Sweedy3960/2414_SPB7_DOC/Doc/others/CalculRTC.docx

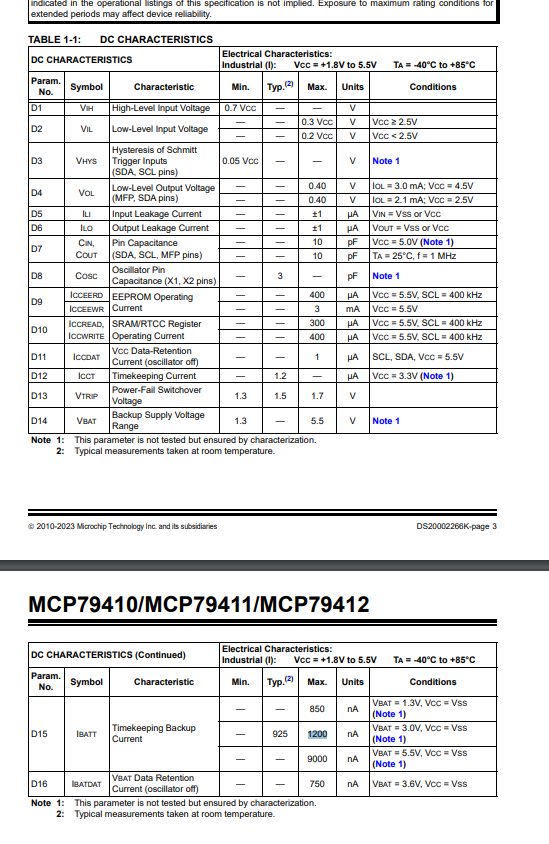
[picture p1: figure]

- Vcap : 1.8 -> 3,3 = 1,5V en 5tau le condo doit diminuer de 1,5V

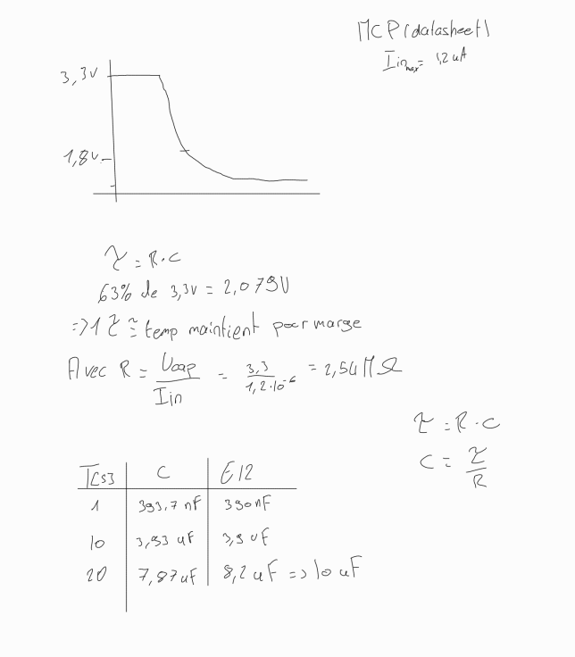
[picture p2: figure]
