Sweedy3960/2414_SPB7_DOC/Doc/others/Capacitive_touch.docx

Rapport de laboratoire

Ecole supérieure

Électronique

Réalisé par :

Aymeric Clauzel

À l’attention de :

Philippe Bovey

Serge Castoldi

Dates :

Début du laboratoire : 5 mars 2024

Fin du laboratoire : 16 avril 2024

Table des matières :

Aucune entrée de table des matières n'a été trouvée.

Sans boitier

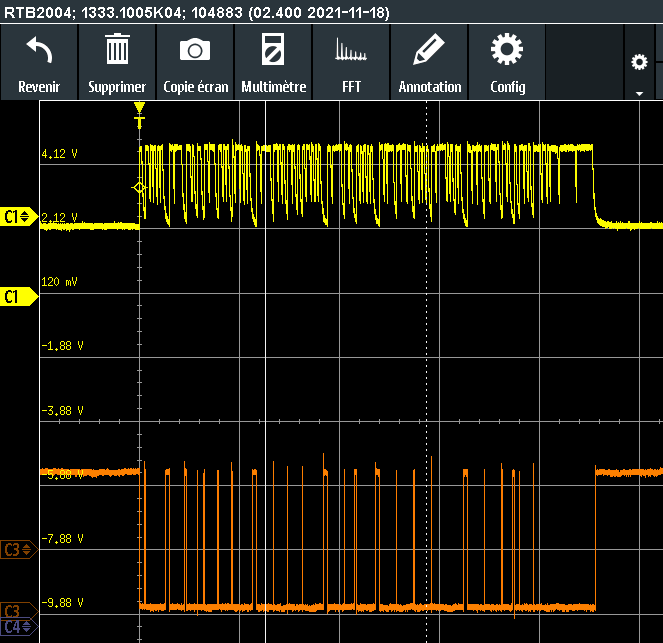
[picture p33: figure]
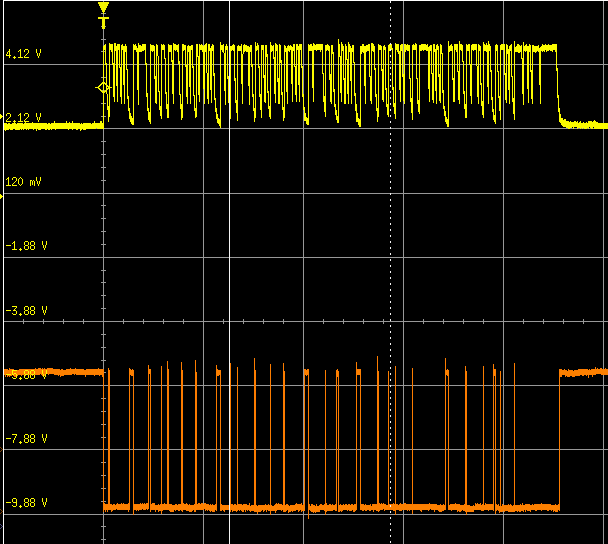
[picture p34: figure]

Pas appuyé | Appuyé

Avec boitier

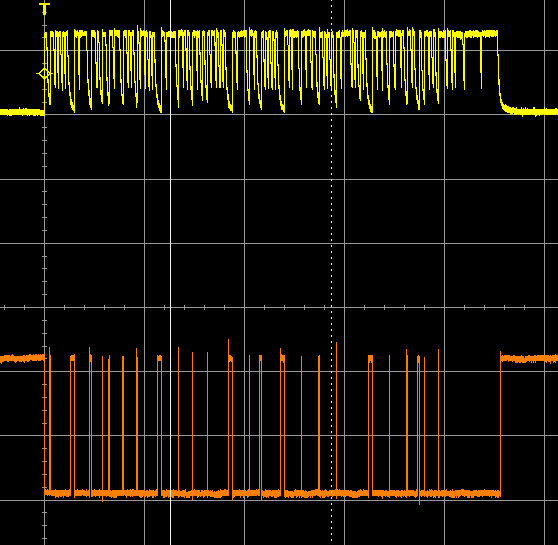
[picture p35: figure]
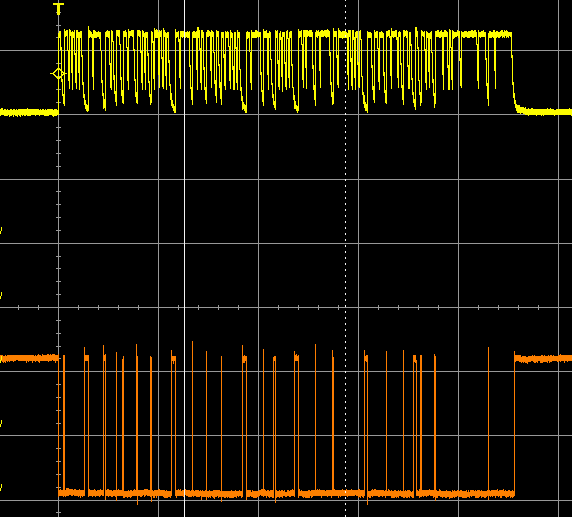
[picture p36: figure]

ACL/NBN Page 1

ETML TP0-LedAd MIN

ETML-Es Modulation FM ELCO
