Sweedy3960/2414_SPB7_DOC/hard/Footprint/ZVP4525ZTA/AltiumDesigner/SOT-89-3_4P5X2P6_DIO.step

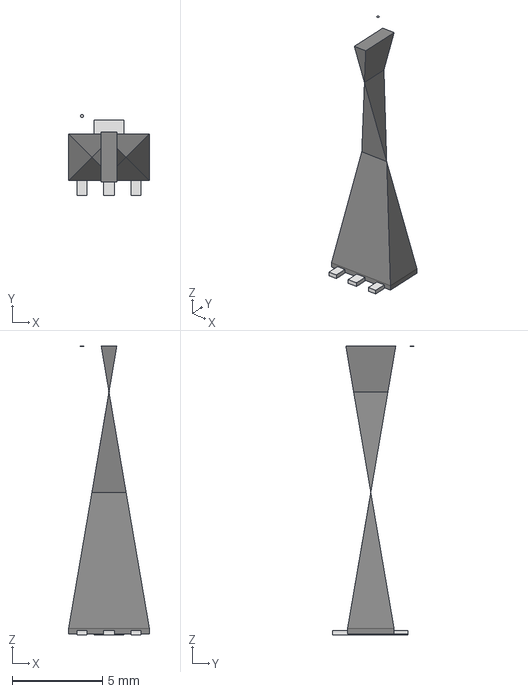
[picture p50: CAD file, 2025-05-13]
hard/Footprint/ZVP4525ZTA/AltiumDesigner/SOT-89-3_4P5X2P6_DIO.step
4.50 x 4.51 x 16.1 mm
