Sweedy3960/2414_SPB7_DOC/Mec/test capa.step

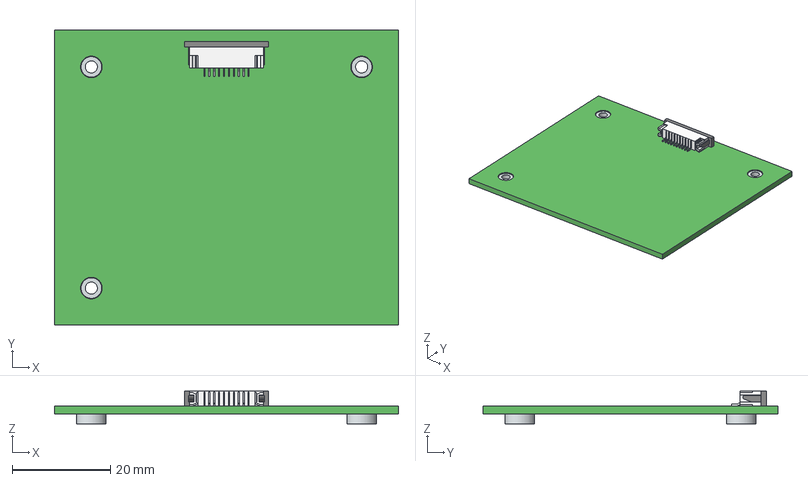
[picture p51: CAD file, 2025-05-13]
Mec/test capa.step
70.0 x 60.0 x 6.63 mm
Geh㴳e_10
Verschluss_10
Pin1 x 10
Pin_rechts
Pin_rechts_mir
