Sweedy3960/2414_SPB7_DOC/Mec/testafrfr.DXF

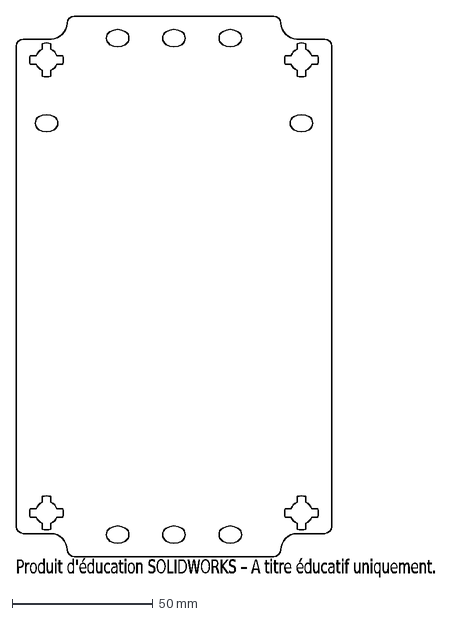
[picture p52: CAD file, 2025-05-13]
Mec/testafrfr.DXF
Produit d'éducation SOLIDWORKS – A titre éducatif uniquement.
