Sweedy3960/2414_SPB7_DOC/Mec/2414_TouchCapa.step

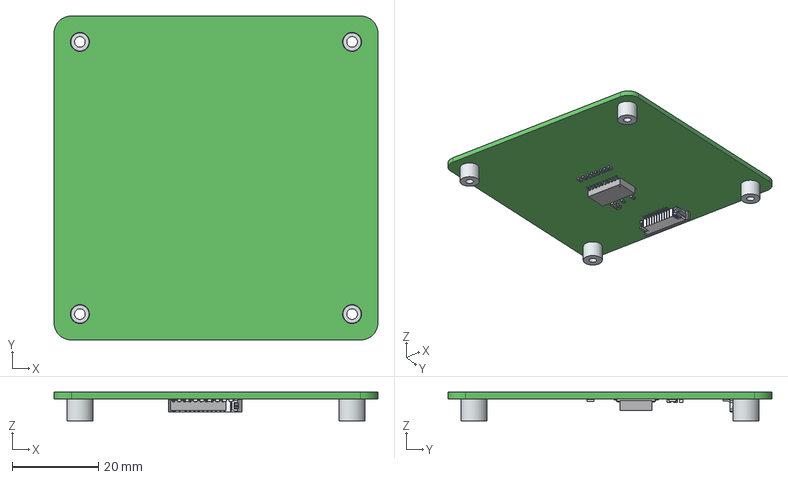
[picture p53: CAD file, 2025-05-13]
Mec/2414_TouchCapa.step
75.0 x 75.0 x 6.61 mm
Mid_Body x 10
Mark x 10
Geh㴳e_10
Verschluss_10
Pin1 x 10
Pin_rechts
Pin_rechts_mir
