Sweedy3960/2414_SPB7_DOC/Mec/PN-1334.STEP

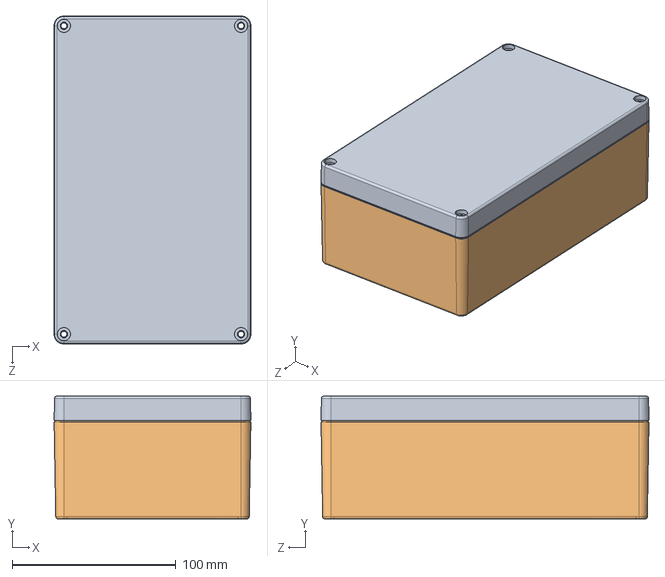
[picture p54: CAD file, 2025-05-13]
Mec/PN-1334.STEP
120.0 x 75.0 x 200.0 mm
1334-C
1334-B
