Sweedy3960/2414_SPB7_DOC/Doc/Project Outputs for 2414_TesteurDeSprinkler_SPB7/DesignDocs/2414_TesteurDeSprinkler_SPB7_Schematic_Variant_No Variations.PDF

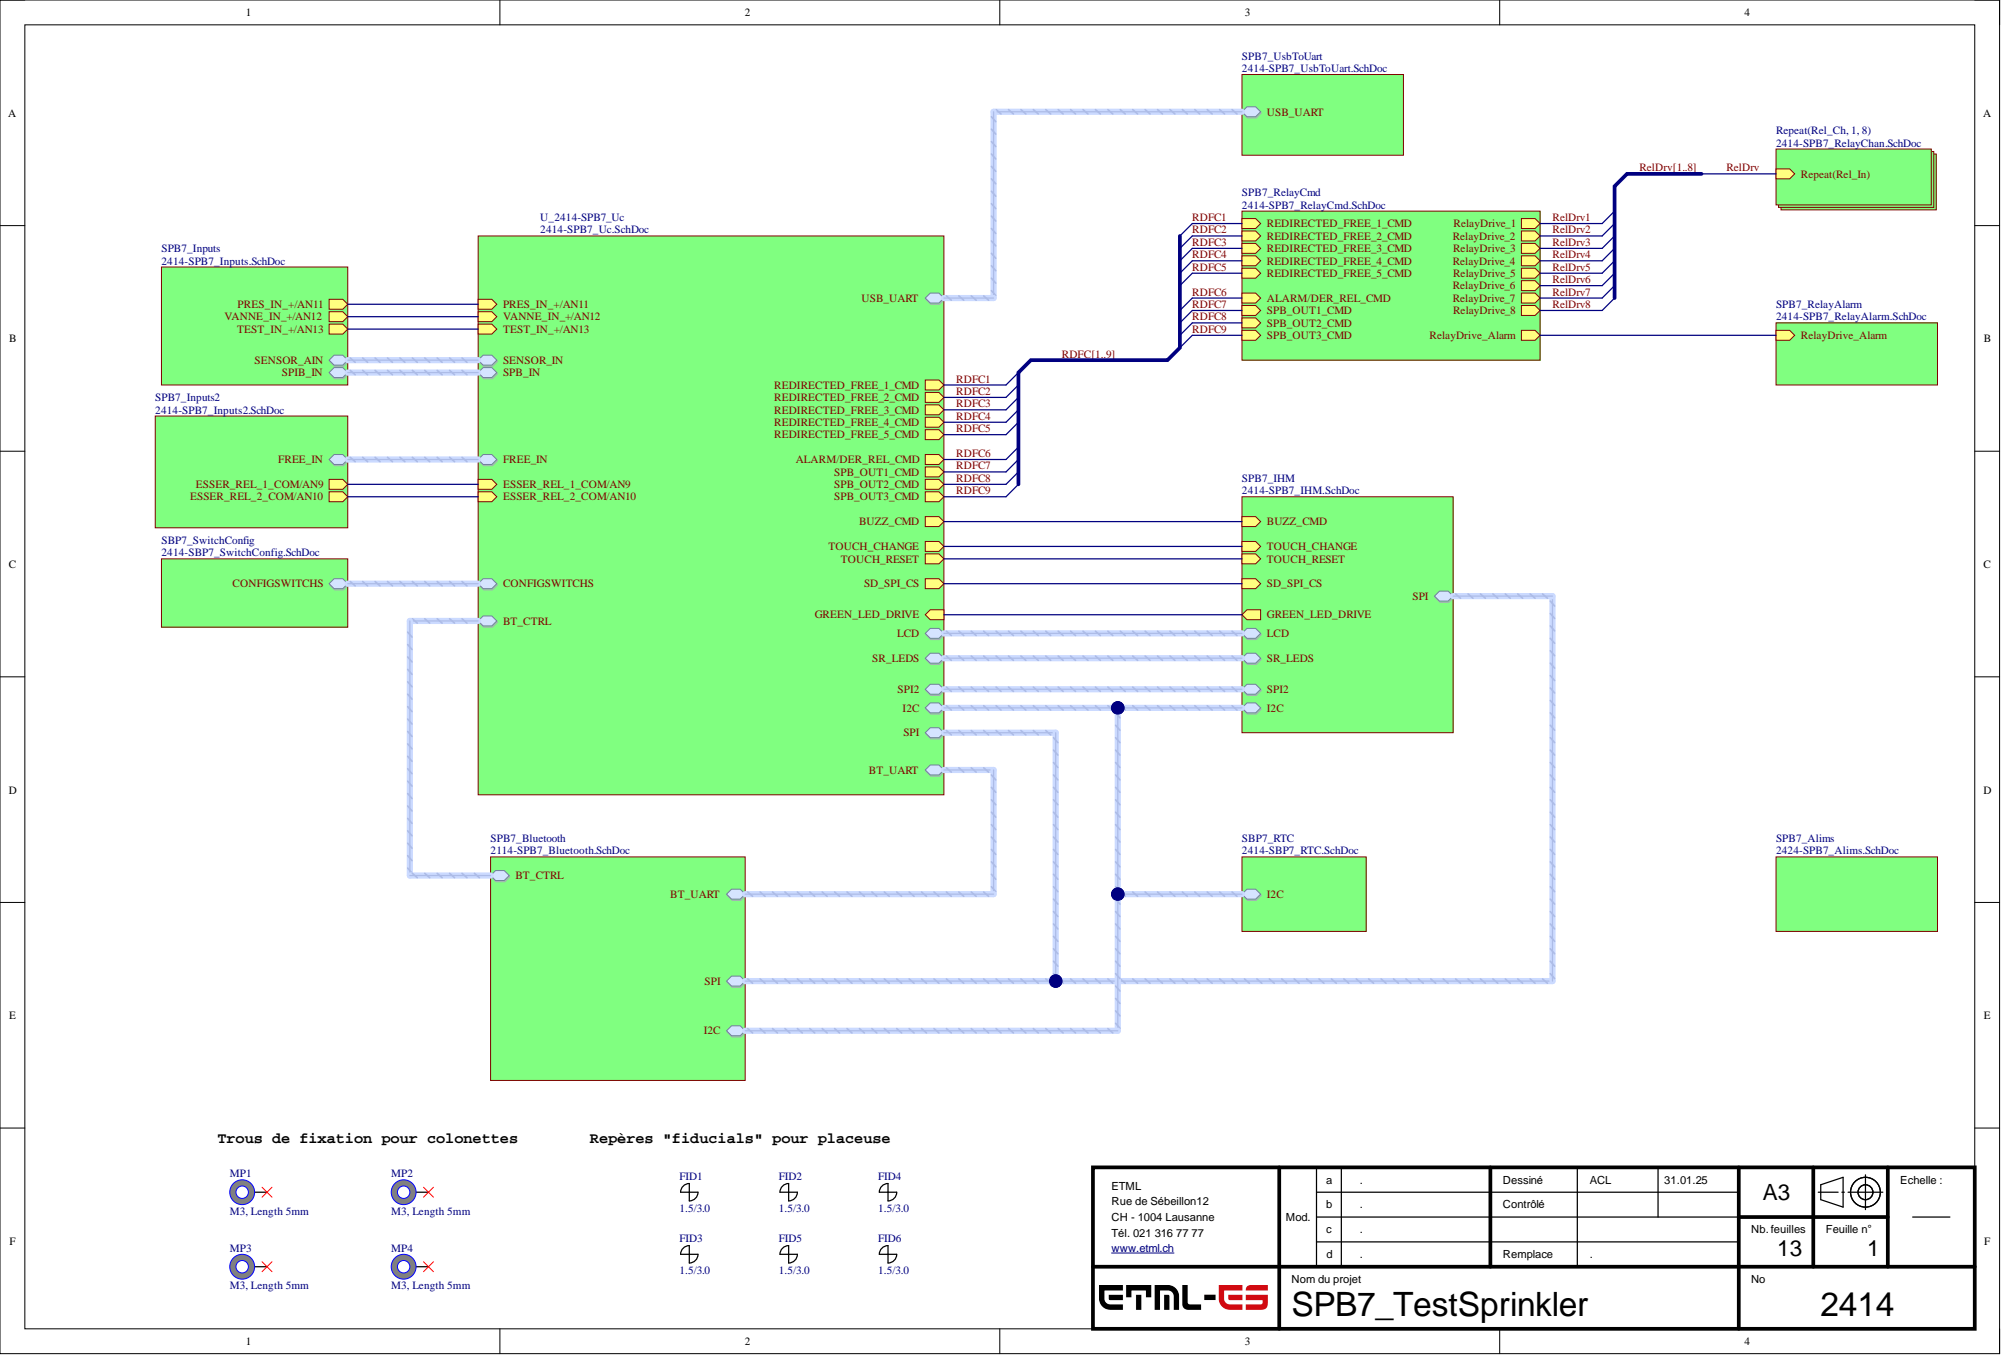
[picture p108: page 1]

ETML Rue de Sébeillon12 CH - 1004 Lausanne Tél. 021 316 77 77 www.etml.ch | Mod. | a | . | Dessiné | ACL | 31.01.25 | A3 | | Echelle :

b | . | Contrôlé

c | . | | | | Nb. feuilles 13 | Feuille n° 1

d | . | Remplace | .

Nom du projet SPB7_TestSprinkler | | | | | | No 2414

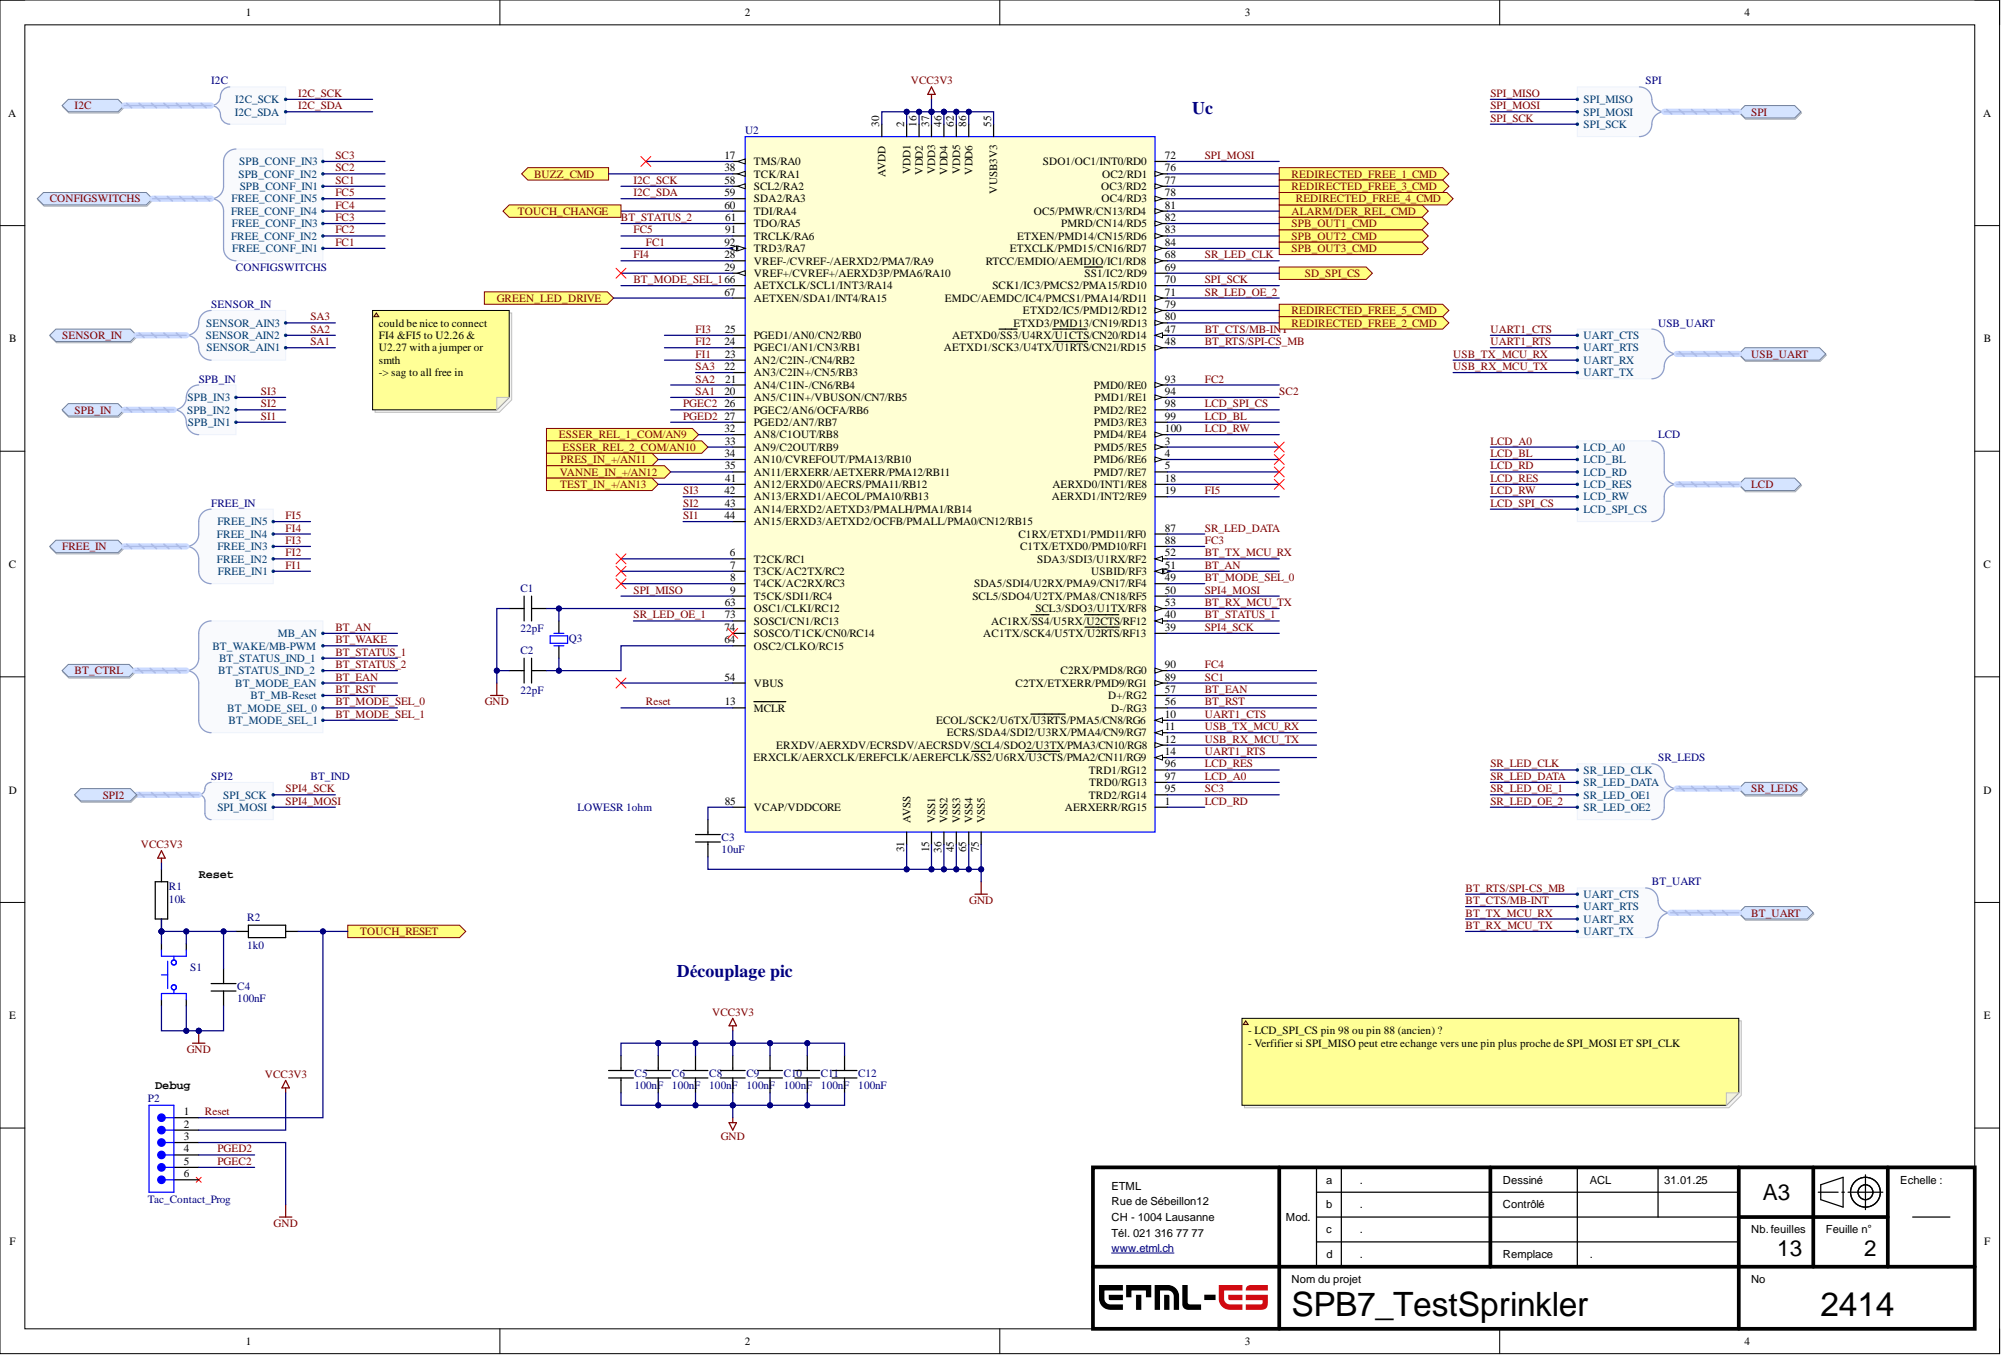
[picture p109: page 2]

ET M L Rue de S ébeillon12 C H - 1004 Lausanne T él. 021 316 77 77 w w w .et m l . c h | Mod . | | | Des s i n é | AC L | 31.01. 2 5 | A3 | | Echelle :

abcd | .... | Cont r ô l é

Nb. feuilles | Feuille n °

Rempla c e | .

Nom du projet SPB7_TestSpr i nkl e r | | | N o 241

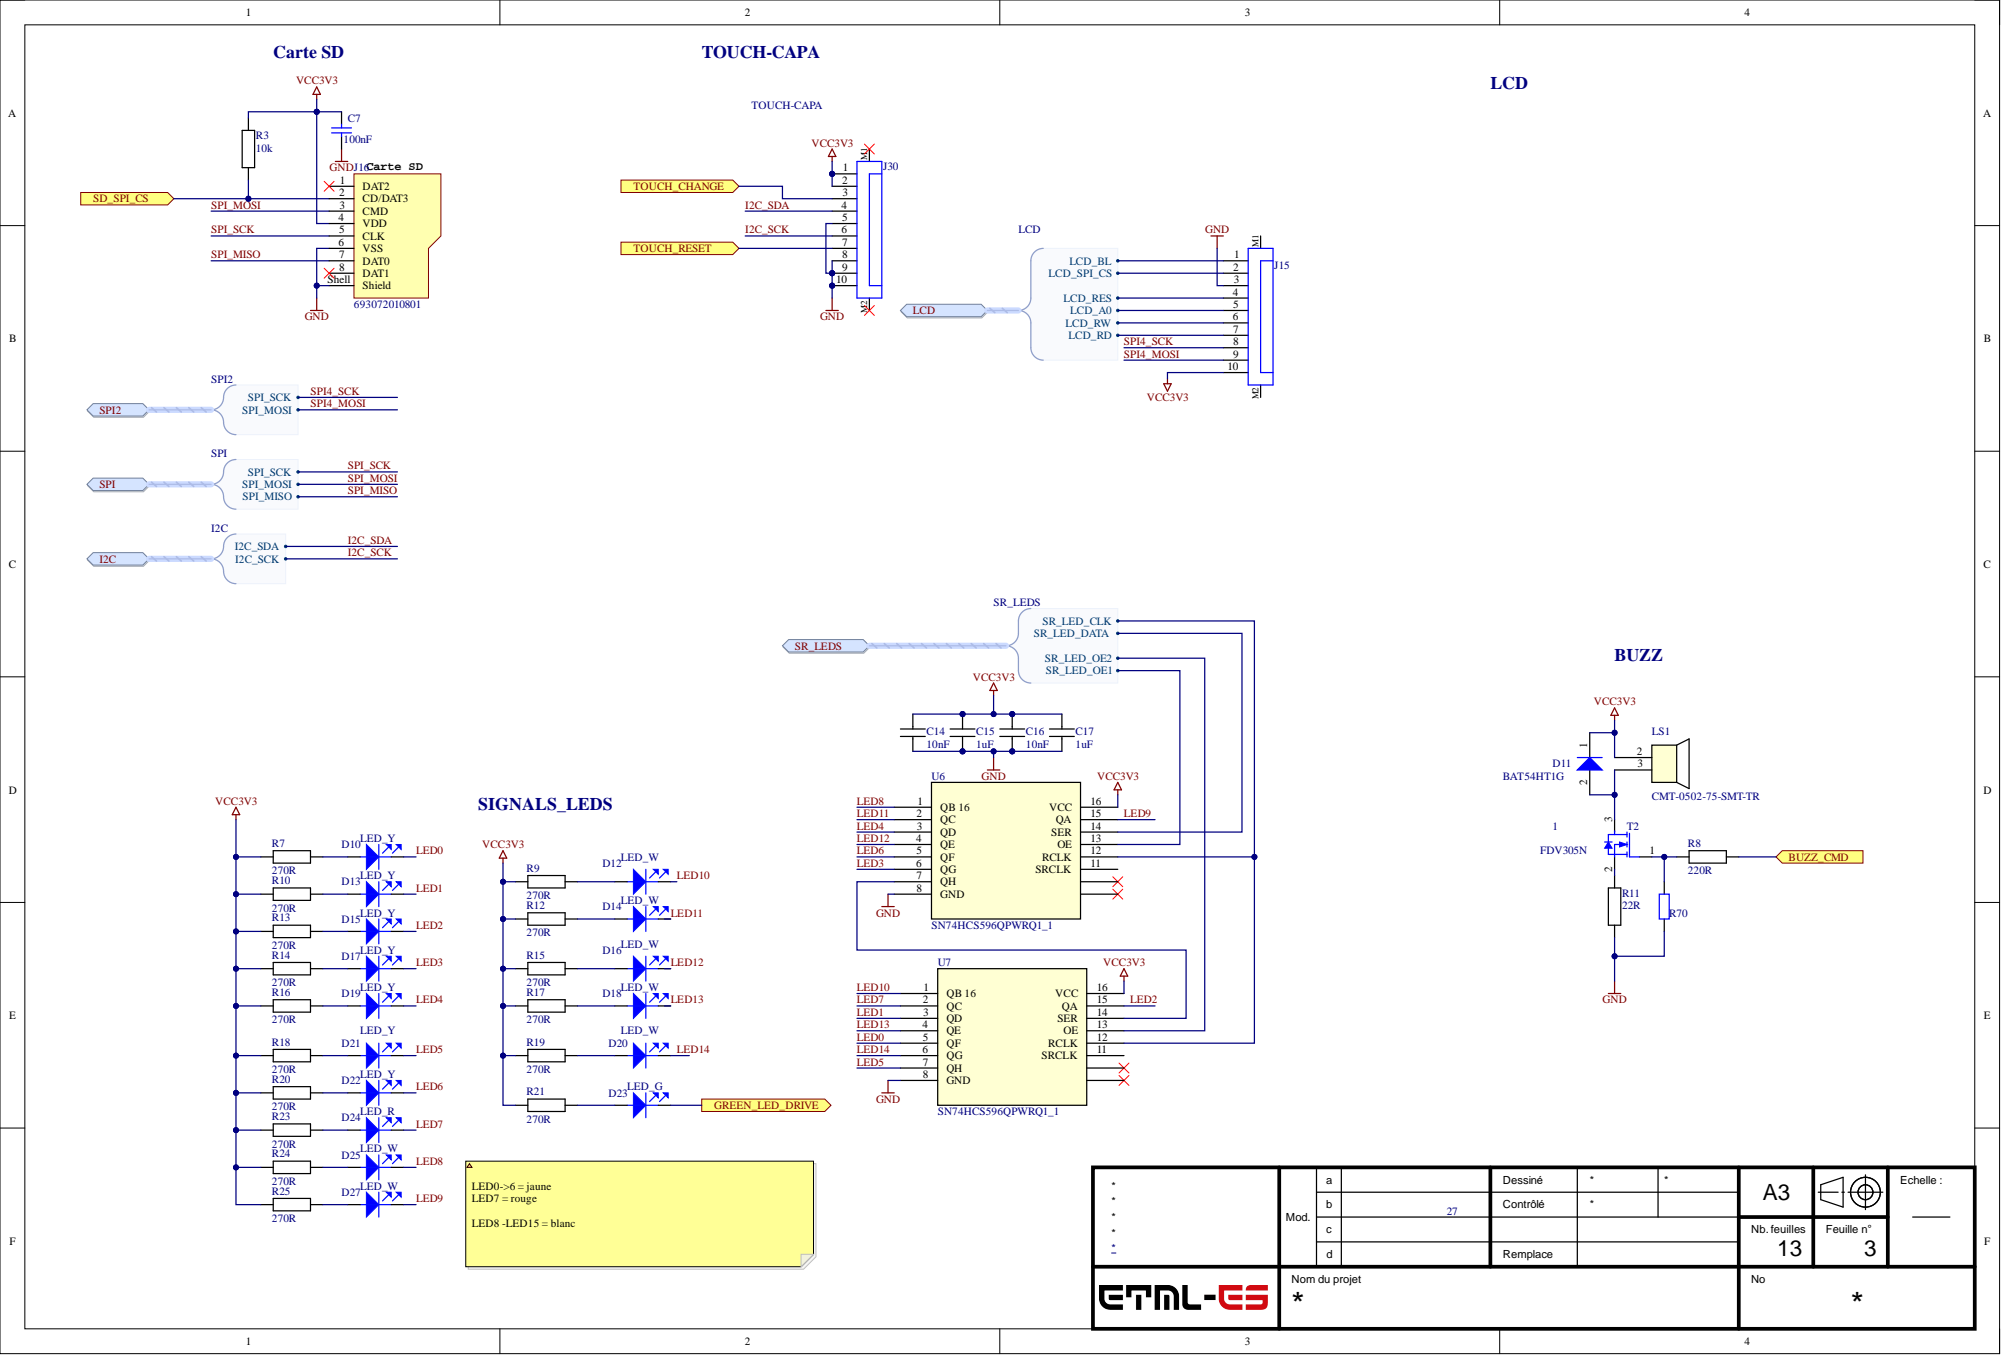
[picture p110: page 3]

* * * * * | Mod. | a | | Dessiné | * | * | A3 | | Echelle :

b | 27 | Contrôlé | *

c | | | | | Nb. feuilles 13 | Feuille n° 3

d | | Remplace

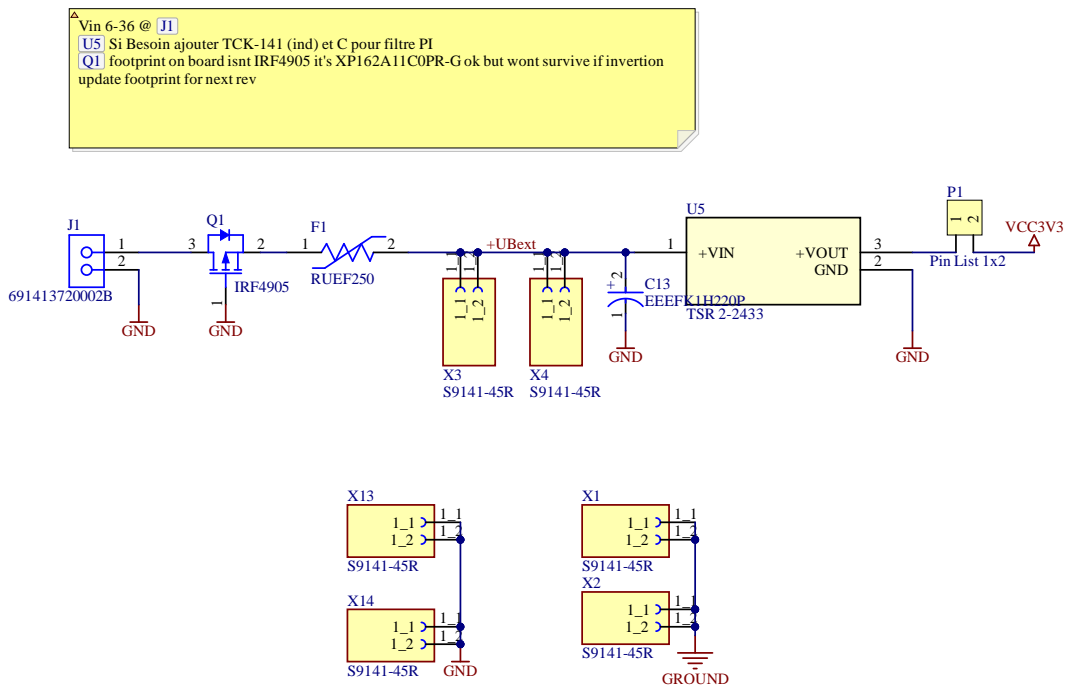
[picture p111: page 4]

Vin 6-36 @ J1
U5 Si Besoin ajouter TCK-141 (ind) et C pour filtre PI
Q1 footprint on board isnt IRF4905 it's XP162A11C0PR-G ok but wont survive if invertion
update footprint for next rev

ETML Rue de Sébeillon12 CH - 1004 Lausanne Tél. 021 316 77 77 www.etml.ch | Mod. | a | . | Dessiné | ACL | 31.01.25 | A4 | | Echelle :

b | . | Contrôlé

c | . | | | | Nb. feuilles 13 | Feuille n° 4

d | . | Remplace | .
SPB7_TestSprinkler | | | | | | 2414

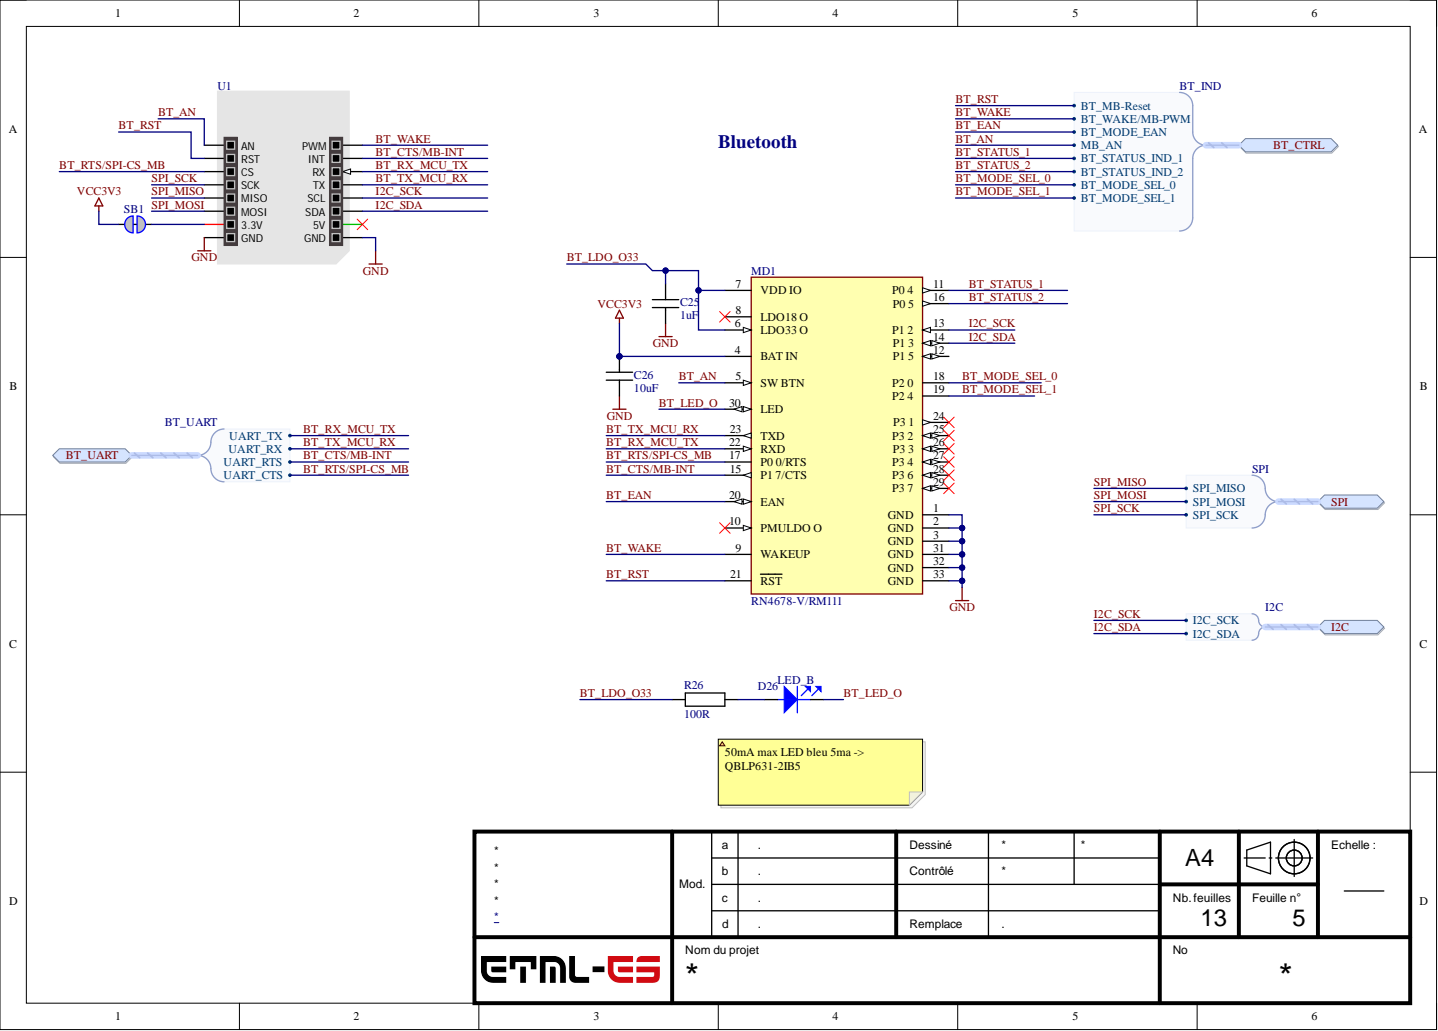
[picture p112: page 5]

* * * * * | Mod. | a | . | Dessiné | * | * | A4 | | Echelle :

b | . | Contrôlé | *

c | . | | | | Nb. feuilles 13 | Feuille n° 5

d | . | Remplace | .

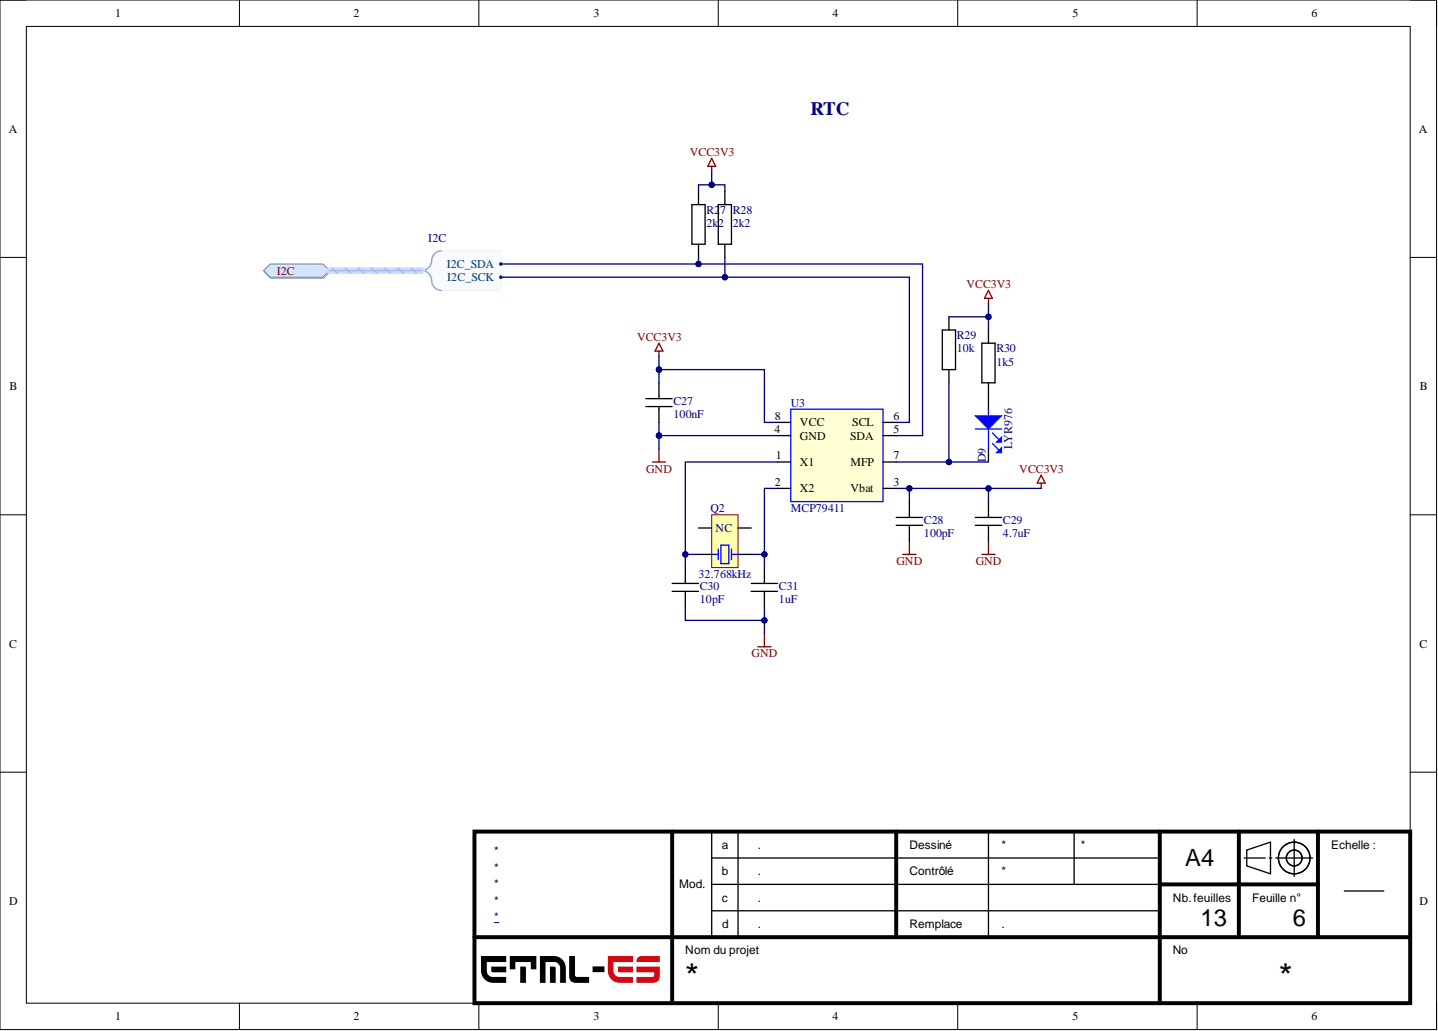
[picture p113: page 6]

3 I2C_SCK

1 | G N D A X 1 MFP X 2 V b at | 7

** *** | Mod . | | | Des s i n é | * | A4 | | Echelle :

abcd | .... | Cont r ô l é

Nb. feuilles 13 | Feuille n ° 6

Rempla c e

Nom du projet * | | N o *

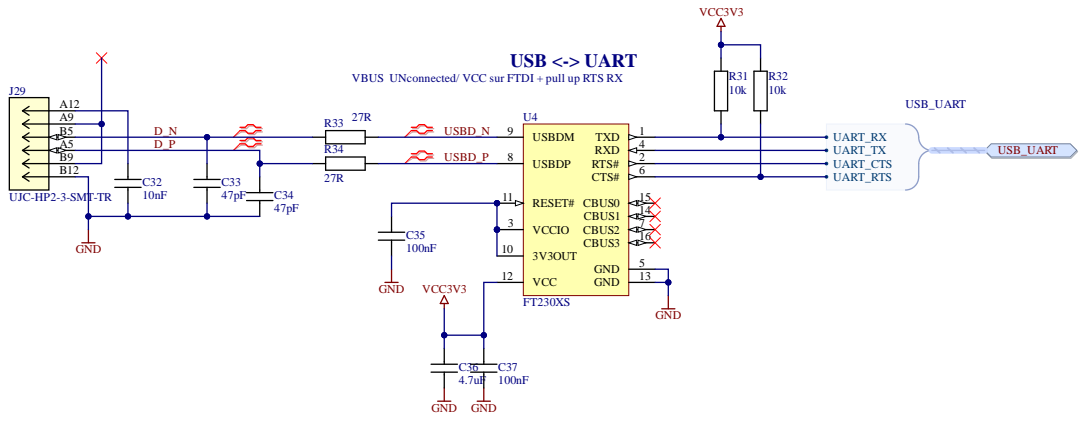
[picture p114: page 7]

** *** | Mod . | | | Des s i n é | * | A4 | | Echelle :

abcd | .... | Cont r ô l é

Nb. feuilles 13 | Feuille n ° 7

Rempla c e

Nom du projet * | | N o *

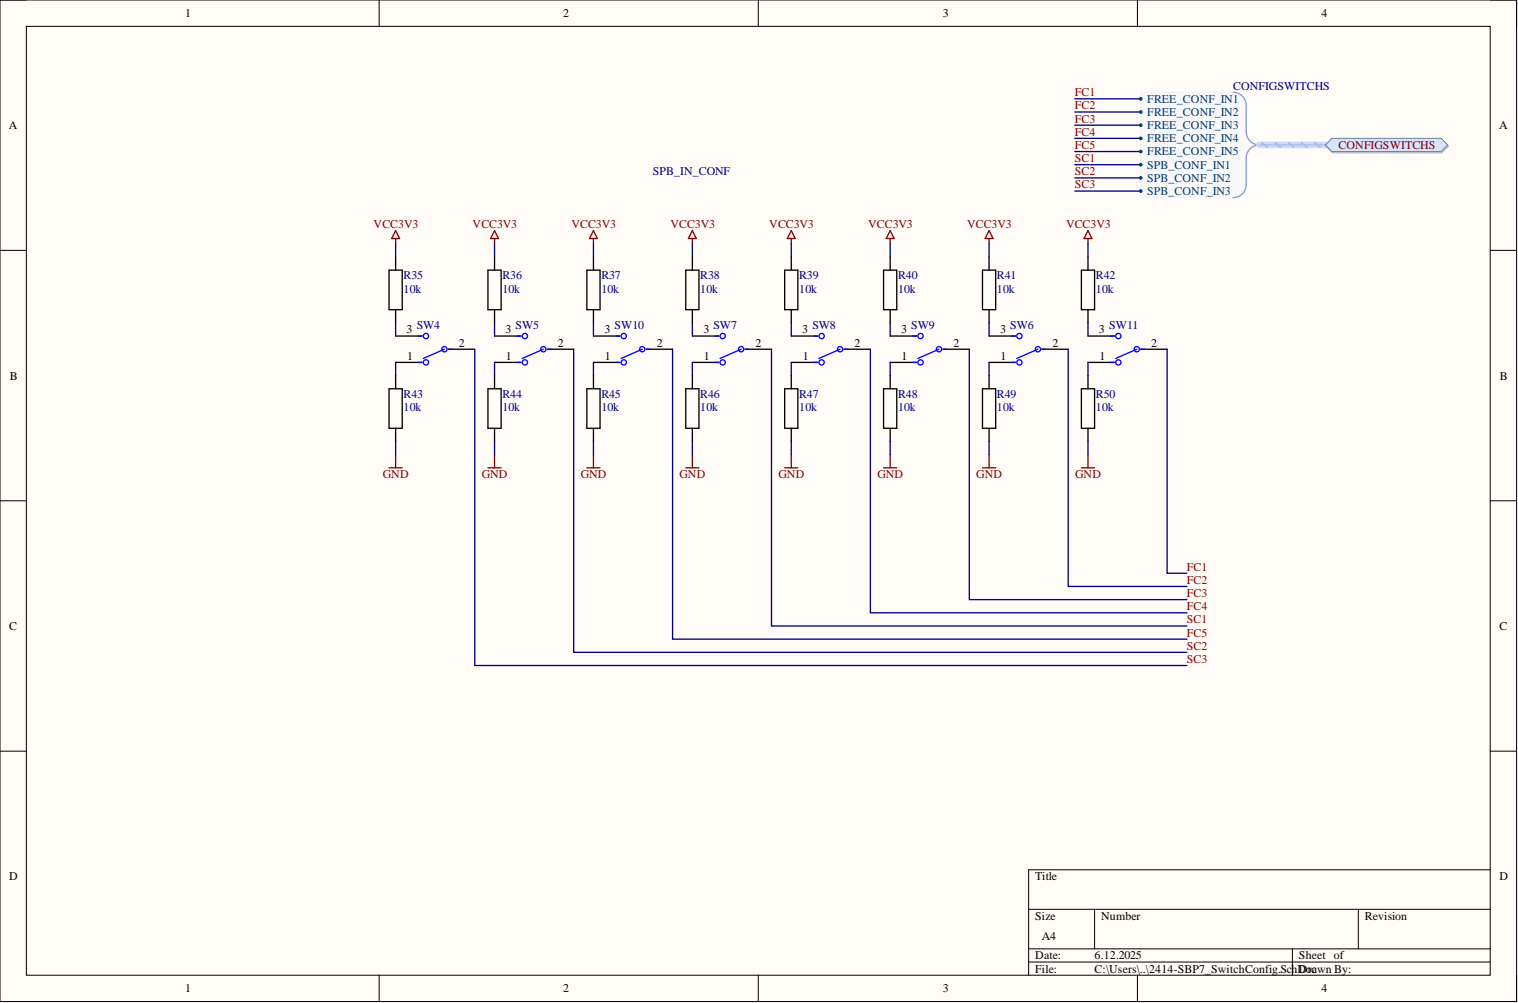
[picture p115: page 8]

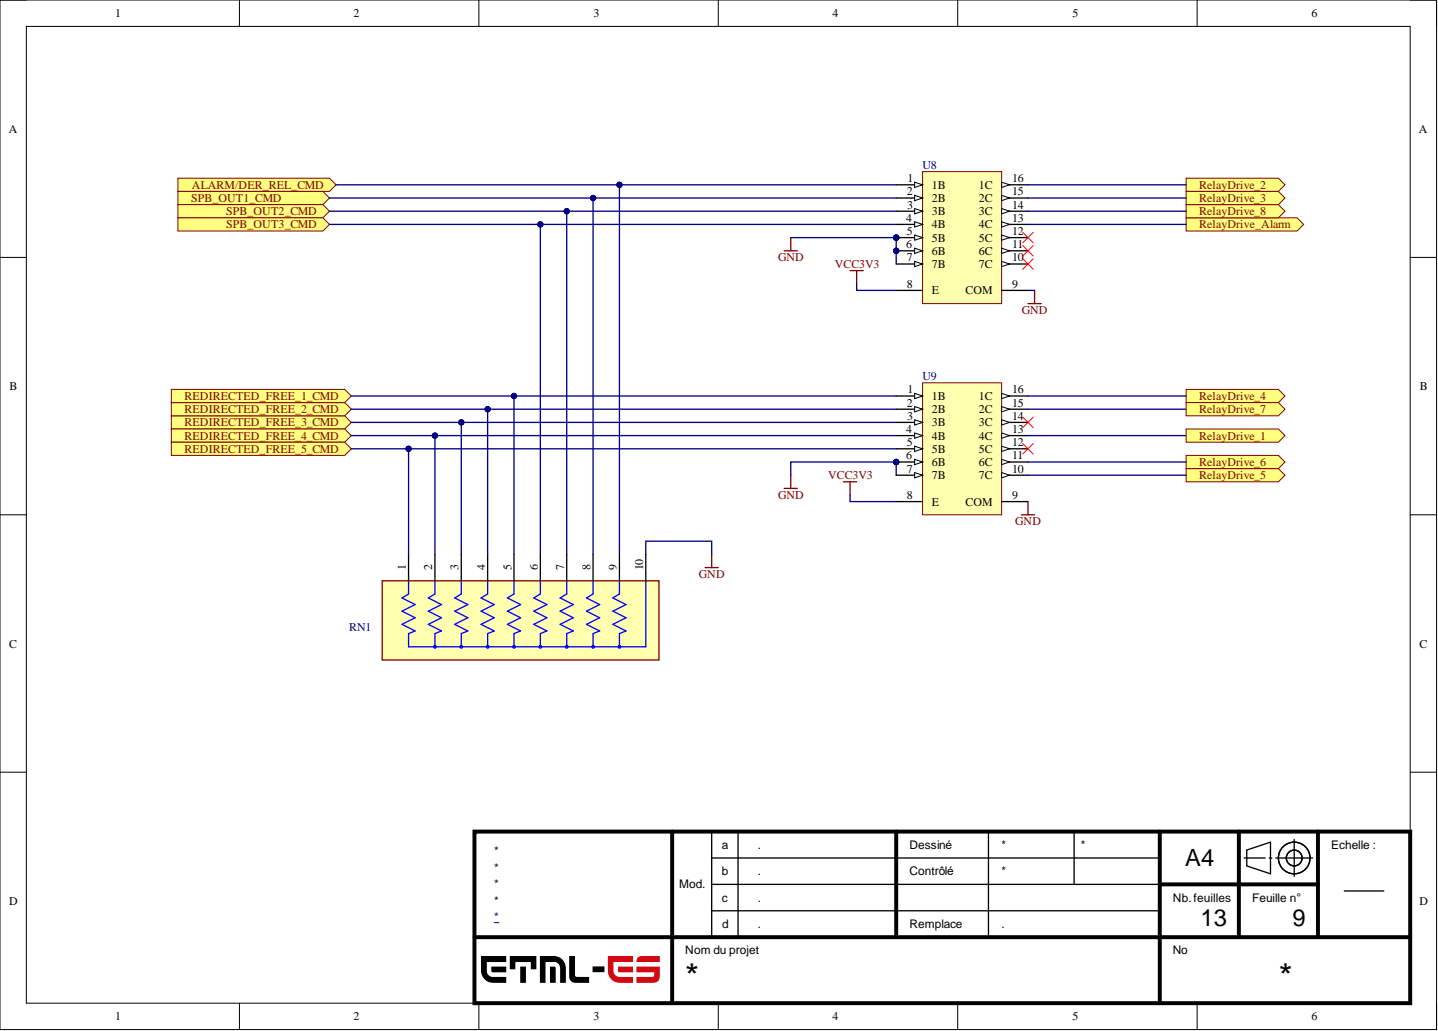
[picture p116: page 9]

* * * * * | Mod. | a | . | Dessiné | * | * | A4 | | Echelle :

b | . | Contrôlé | *

c | . | | | | Nb. feuilles 13 | Feuille n° 9

d | . | Remplace | .

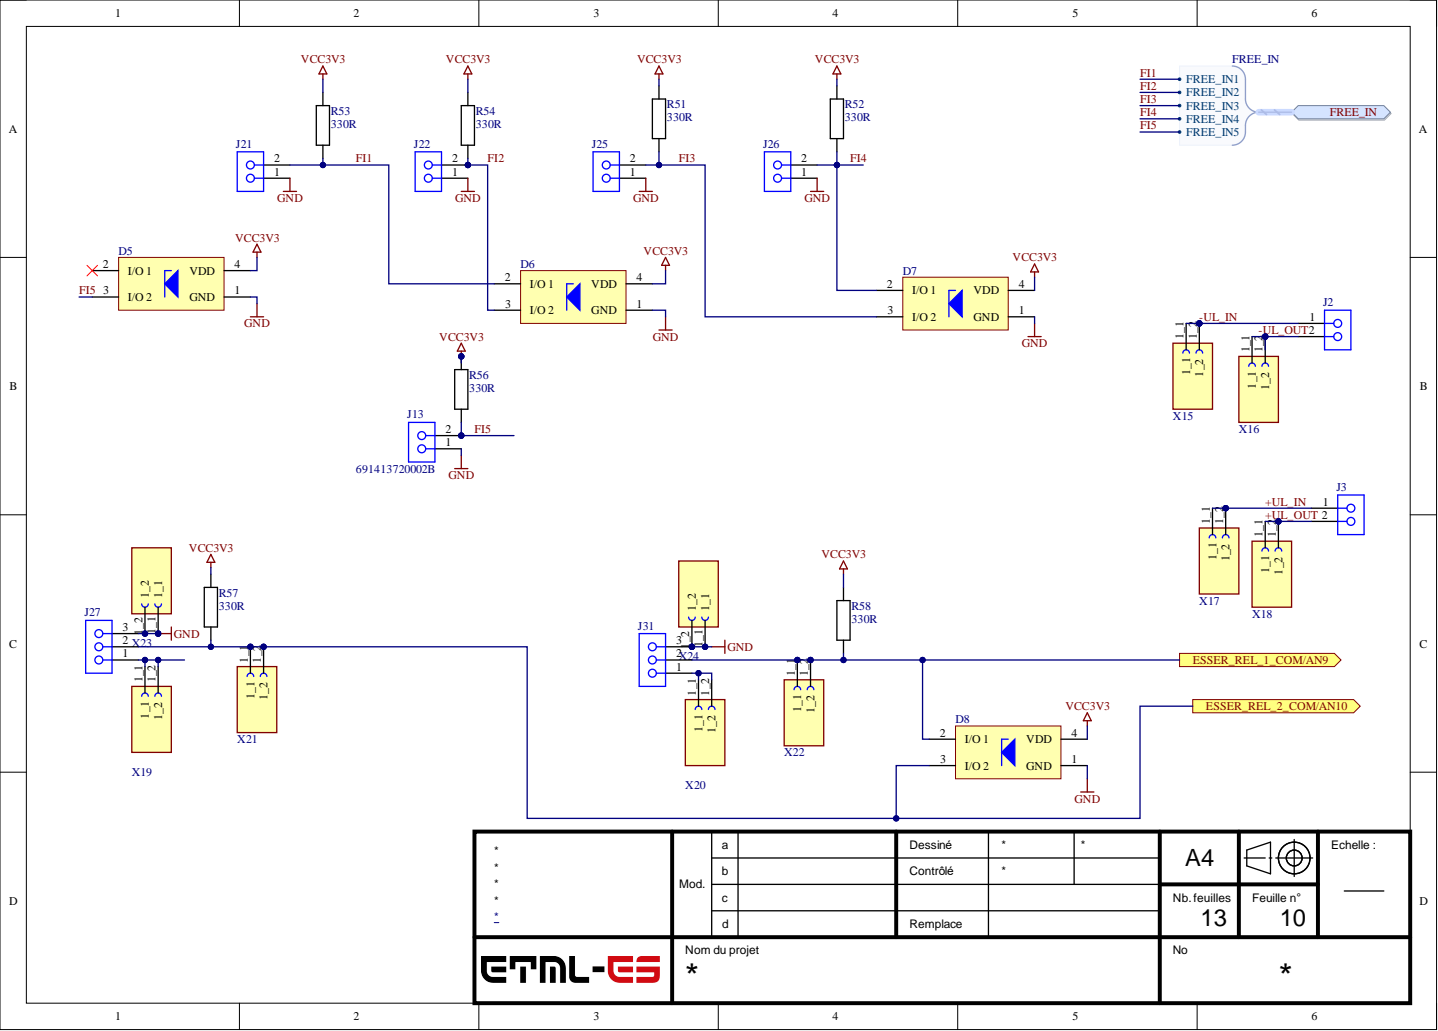
[picture p117: page 10]

-UL_OUT 2

* * * * * | Mod. | a | Dessiné | * | * | A4 | | Echelle :

b | Contrôlé | *

c | | | | Nb. feuilles 13 | Feuille n° 10

d | Remplace

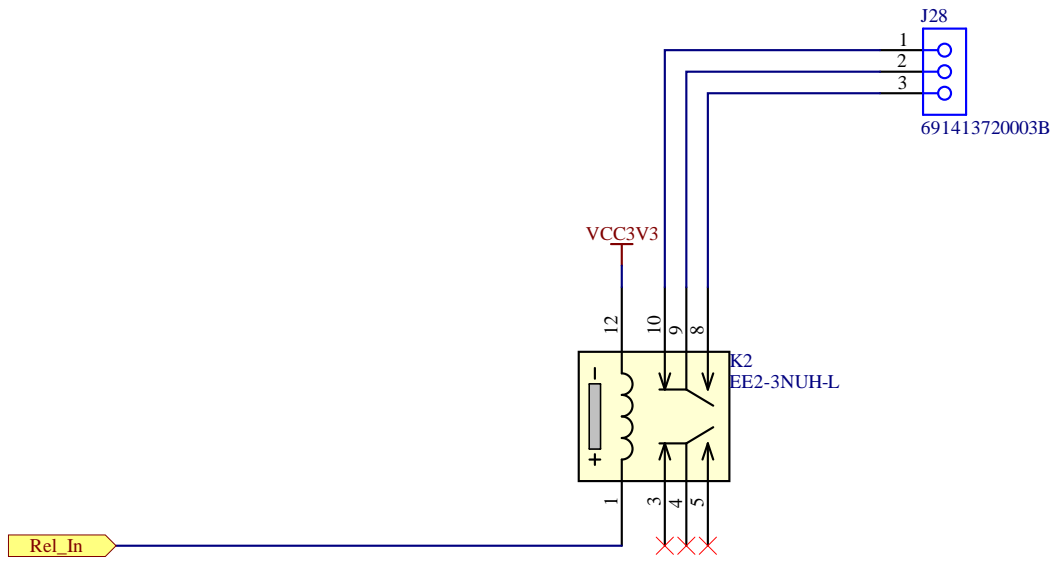
[picture p118: page 11]

** *** | Mod . | | Des s i n é | ** | * | A4 | | Echelle :

abcd | Cont r ô l é

Nb. feuilles 13 | Feuille n ° 1 1

Rempla c e

Nom du projet * | | N o *

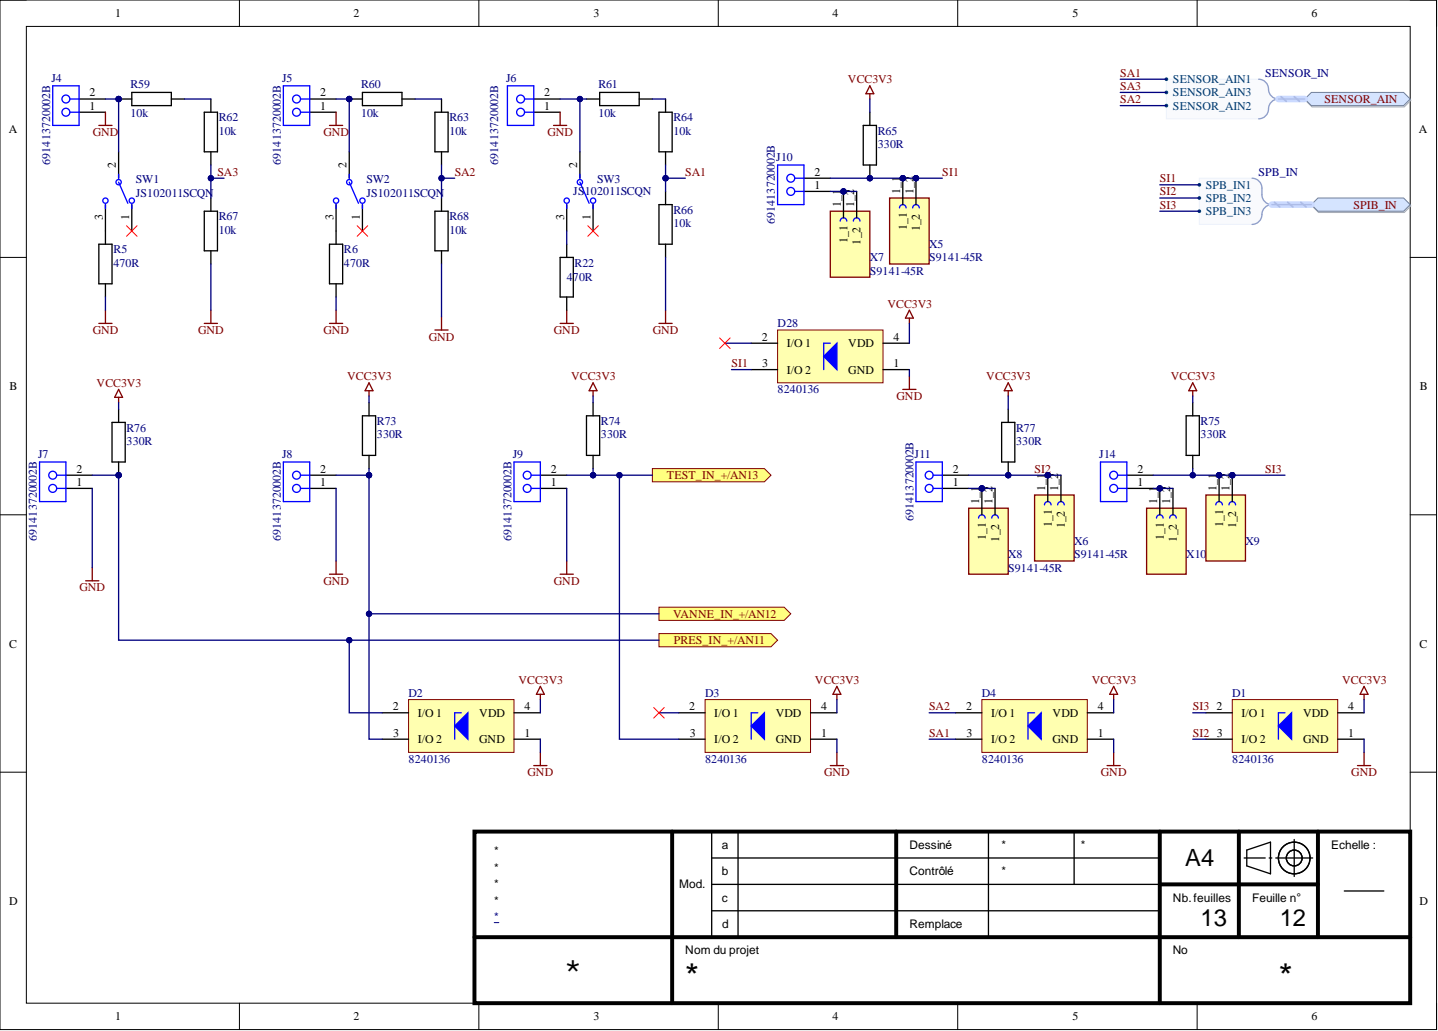
[picture p119: page 12]

* * * * * | Mod. | a | Dessiné | * | * | A4 | | Echelle :

b | Contrôlé | *

c | | | | Nb. feuilles 13 | Feuille n° 12

d | Remplace

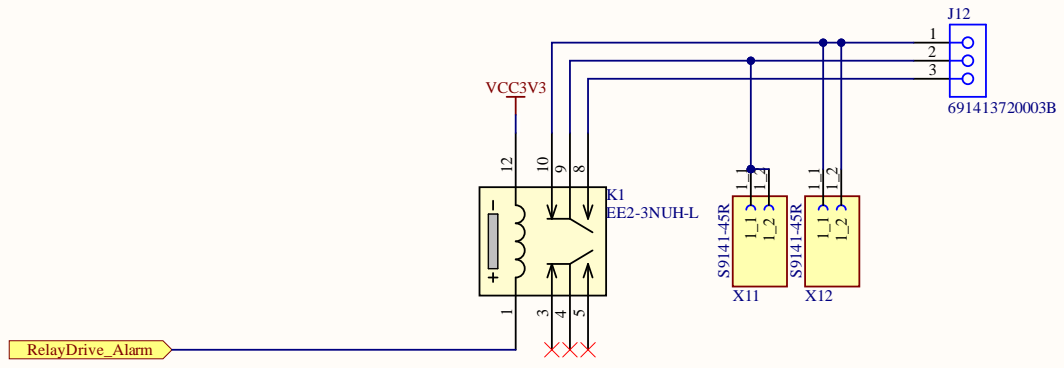
[picture p120: page 13]
