Sweedy3960/2414_SPB7_DOC/Doc/2414_TesteurDeSprinklerplanif.xlsx

No semaine projet |  | 1 | 2 | 3 | 4 | 5 | 6 | V | V | 7 | 8 | 9 | 10 | 11 | 12 | V | 13 | 14 | 15 | 16 | 17 | 18 | 19 | V | V | 20 | 21 | 22 | 23 | V | 24 | 25 | 26 | V
No semaine |  | 47 | 48 | 49 | 50 | 51 | 52 | V | V | 2 | 3 | 4 | 5 | 6 | 7 | V | 9 | 10 | 11 | 12 | 13 | 14 | 15 | V | V | 18 | 20 | 22 | 24 | V | 23 | 24 | 25 | V
Date |  | 2024-11-15 | 2024-11-22 | 2024-11-29 | 2024-12-06 | 2024-12-13 | 2024-12-20 | 2024-12-27 | 2025-01-03 | 2025-01-10 | 2025-01-17 | 2025-01-24 | 2025-01-31 | 2025-02-07 | 2025-02-14 | 2025-02-21 | 2025-02-28 | 2025-03-07 | 2025-03-14 | 2025-03-21 | 2025-03-28 | 2025-04-04 | 2025-04-11 | 2025-04-18 | 2025-04-25 | 2025-05-02 | 2025-05-09 | 2025-05-16 | 2025-05-23 | 2025-05-30 | 2025-06-06 | 2025-06-13 | 2025-06-20 | 2025-06-27
Pré-étude | Consigne |  |  |  | R | P
 | Planifié
 | Réel
Design + Schéma | Consigne |  |  |  |  |  |  |  |  |  |  | R | P
 | Planifié
 | Réel
PCB | Consigne |  |  |  |  |  |  |  |  |  |  |  |  |  |  |  |  |  |  |  | R
 | Planifié
 | Réel
Montage | Consigne |  |  |  |  |  |  |  |  |  |  |  |  |  |  |  |  |  |  |  |  |  |  |  |  |  |  |  |  |  |  |  |  | V
 | Planifié
 | Réel
Softwares | Consigne
 | Planifié
 | Réel
Tests et mise au point | Consigne
 | Planifié
 | Réel
Rédaction du rapport | Consigne
 | Planifié
 | Réel
Préparation présentation + démo | Consigne
 | Planifié
 | Réel
Présentations | Consigne |  |  |  |  |  |  |  |  |  |  |  |  |  |  |  |  |  |  |  |  |  |  |  |  |  |  |  |  |  |  | R | P
 | Planifié
 | Réel
Finitions/corrections/documentation | Consigne
 | Planifié
 | Réel
Projet
2414_TesteurDeSprinkler
Auteur
Aymeric clauzel
Date de création
2024-01-22
