Sweedy3960/2414_SPB7_DOC/Doc/Grille EVALUATION proj v1-1 modèle.xlsx

Génie électrique
Formulaire d'évaluation de projet
Candidat |  | Modèle
Enseignant responsable |  | Serge CASTOLDI
Enseignant assistant |  | José MORENO
 |  |  |  |  |  | coeff.
 |  |  | 1. Pré-étude (0.5) | #DIV/0! |  | 1
 |  |  | 2. Design (0.5) | #DIV/0! |  | 1
 |  |  | 3a. Réalisation hardware (0.5) | #DIV/0! |  | 2
 |  |  | 3b. Réalisation software (0.5) | #DIV/0! |  | 2
 |  |  | 3c. Dossier (0.5) | #DIV/0! |  | 2
 |  |  | 4. Présentation finale (0.5) | #DIV/0! |  | 1
 |  |  | 5. Attitude (0.5) | #DIV/0! |  | 1
 |  |  | Note obtenue (0.1) | #DIV/0!
Prière de remplir tout ou partie des cases vertes svp.
N° | Partie évaluée | Compétence | Indicateur / Critère de réussite |  | Evaluation A, B, C, D |  |  |  |  | Indicateur valide | Nbre pts max | Nbre pts compétence obtenus | Nbre pts compétence maximum | Pourcentage de compétence
1 | Pré-étude : présentation et dossier | 1.1 Capacité à présenter un sujet par oral | Expression : Le candidat s'exprime clairement, avec le bon langage. Compréhension aisée Qualité de la présentation : Moyens utilisés de manière appropriée, temps respecté |  |  |  | 3 | A |  | FALSE |  | 0 | 0 | #DIV/0!
 |  |  |  |  |  |  | 2 | B
 |  |  |  |  |  |  | 1 | C
 |  |  |  |  |  |  | 0 | D
 |  | 1.2 Maîtrise orale du sujet | Contenu technique : Contenu correct, concis, argumentation convaincante, voie présentée envisageable et maîtrisée Réponses aux questions : Le candidat répond clairement et correctement aux questions |  |  |  | 6 | A |  | FALSE
 |  |  |  |  |  |  | 4 | B
 |  |  |  |  |  |  | 2 | C
 |  |  |  |  |  |  | 0 | D
 |  | 1.3 Capacité à présenter un sujet par écrit | Expression : Le candidat s'exprime clairement, avec le bon langage. Compréhension aisée. Qualité du dossier : forme et structure complètes et cohérentes |  |  |  | 3 | A |  | FALSE
 |  |  |  |  |  |  | 2 | B
 |  |  |  |  |  |  | 1 | C
 |  |  |  |  |  |  | 0 | D
 |  | 1.4 Maîtrise écrite du sujet | Qualité du dossier : Contenu correct, concis, argumentation convaincante, voie présentée envisageable et maîtrisée |  |  |  | 9 | A |  | FALSE
 |  |  |  |  |  |  | 6 | B
 |  |  |  |  |  |  | 3 | C
 |  |  |  |  |  |  | 0 | D
 |  | 1.5 Rapidité d'exécution | Travail accompli : Le candidat a fourni une quantité de travail conforme à ce qu'on pouvait raisonnablement attendre de lui. |  |  |  | 3 | A |  | FALSE
 |  |  |  |  |  |  | 2 | B
 |  |  |  |  |  |  | 1 | C
 |  |  |  |  |  |  | 0 | D
 |  | Remarques | 1.1 1.2 1.3 1.4 1.5
N° | Partie évaluée | Compétence | Indicateur / Critère de réussite |  | Evaluation A, B, C, D |  |  |  |  | Indicateur valide | Nbre pts max | Nbre pts compétence obtenus | Nbre pts compétence maximum | Pourcentage de compétence
2 | Design : présentation et dossier | 2.1 Capacité à présenter un sujet par oral | Expression : Le candidat s'exprime clairement, avec le bon langage. Compréhension aisée Qualité de la présentation : Moyens utilisés de manière appropriée, temps respecté |  |  |  | 3 | A |  | FALSE |  | 0 | 0 | #DIV/0!
 |  |  |  |  |  |  | 2 | B
 |  |  |  |  |  |  | 1 | C
 |  |  |  |  |  |  | 0 | D
 |  | 2.2 Maîtrise orale du sujet | Contenu technique : Contenu correct, concis, argumentation convaincante, voie présentée envisageable et maîtrisée Réponses aux questions : Le candidat répond clairement et correctement aux questions |  |  |  | 6 | A |  | FALSE
 |  |  |  |  |  |  | 4 | B
 |  |  |  |  |  |  | 2 | C
 |  |  |  |  |  |  | 0 | D
 |  | 2.3 Capacité à présenter un sujet par écrit | Expression : Le candidat s'exprime clairement, avec le bon langage. Compréhension aisée. Qualité du dossier : forme et structure, contenu complet et cohérent |  |  |  | 3 | A |  | FALSE
 |  |  |  |  |  |  | 2 | B
 |  |  |  |  |  |  | 1 | C
 |  |  |  |  |  |  | 0 | D
 |  | 2.4 Maîtrise écrite du sujet | Qualité du dossier : Contenu correct, concis, argumentation convaincante, voie présentée envisageable et maîtrisée |  |  |  | 9 | A |  | FALSE
 |  |  |  |  |  |  | 6 | B
 |  |  |  |  |  |  | 3 | C
 |  |  |  |  |  |  | 0 | D
 |  | 2.5 Rapidité d'exécution | Travail accompli : Le candidat a fourni une quantité de travail conforme à ce qu'on pouvait raisonnablement attendre de lui. |  |  |  | 3 | A |  | FALSE
 |  |  |  |  |  |  | 2 | B
 |  |  |  |  |  |  | 1 | C
 |  |  |  |  |  |  | 0 | D
 |  | Remarques | 2.1 2.2 2.3 2.4 2.5
N° | Partie évaluée | Compétence | Indicateur / Critère de réussite |  | Evaluation A, B, C, D |  |  |  |  | Indicateur valide | Nbre pts max | Nbre pts compétence obtenus | Nbre pts compétence maximum | Pourcentage de compétence
3a | Réalisation hardware | 3a.1 Réalisation CAO | Qualité professionnelle de la réalisation CAO. Réutilisable. Documenté. Tous les documents permettant la construction d'une pièce sont disponibles. |  |  |  | 3 | A |  | FALSE |  | 0 | 0 | #DIV/0!
 |  |  |  |  |  |  | 2 | B
 |  |  |  |  |  |  | 1 | C
 |  |  |  |  |  |  | 0 | D
 |  | 3a.2 Montage, mise en service, mise au point | Qualité professionnelle du montage (brasures, placement composants, etc). Nombre et importances des modifications, patchs, etc |  |  |  | 3 | A |  | FALSE
 |  |  |  |  |  |  | 2 | B
 |  |  |  |  |  |  | 1 | C
 |  |  |  |  |  |  | 0 | D
 |  | 3a.3 Atteinte des objectifs | Niveau de fonctionnement / Fonctionnalités implementées : Cahier des charges rempli/remplissable avec le hardware présenté. |  |  |  | 3 | A |  | FALSE
 |  |  |  |  |  |  | 2 | B
 |  |  |  |  |  |  | 1 | C
 |  |  |  |  |  |  | 0 | D
 |  | Remarques | 3a.1 3a.2 3a.3
N° | Partie évaluée | Compétence | Indicateur / Critère de réussite |  | Evaluation A, B, C, D |  |  |  |  | Indicateur valide | Nbre pts max | Nbre pts compétence obtenus | Nbre pts compétence maximum | Pourcentage de compétence
3b | Réalisation software | 3b.1 Codage | Qualité professionnelle du codage, algorithmique. (Tous les programmes sont évalués : uC, application PC, autre) |  |  |  | 9 | A |  | FALSE |  | 0 | 0 | #DIV/0!
 |  |  |  |  |  |  | 6 | B
 |  |  |  |  |  |  | 3 | C
 |  |  |  |  |  |  | 0 | D
 |  | 3b.2 Documentation du code | Code réutilisable. Documenté. (Tous les programmes sont évalués : uC, application PC, autre) |  |  |  | 3 | A |  | FALSE
 |  |  |  |  |  |  | 2 | B
 |  |  |  |  |  |  | 1 | C
 |  |  |  |  |  |  | 0 | D
 |  | 3b.3 Atteinte des objectifs | Niveau de fonctionnement / Fonctionnalités implementées : Cahier des charges rempli/remplissable avec le(les) software(s) présenté(s). |  |  |  | 6 | A |  | FALSE
 |  |  |  |  |  |  | 4 | B
 |  |  |  |  |  |  | 2 | C
 |  |  |  |  |  |  | 0 | D
 |  | Remarques | 3b.1 3b.2 3b.3
N° | Partie évaluée | Compétence | Indicateur / Critère de réussite |  | Evaluation A, B, C, D |  |  |  |  | Indicateur valide | Nbre pts max | Nbre pts compétence obtenus | Nbre pts compétence maximum | Pourcentage de compétence
3c | Dossier | 3c.1 Capacité à présenter un sujet par écrit | Expression : Le candidat s'exprime clairement, avec le bon langage. Compréhension aisée. Qualité du dossier : forme et structure, contenu complet (y compris annexes demandées) et cohérent |  |  |  | 6 | A |  | FALSE |  | 0 | 0 | #DIV/0!
 |  |  |  |  |  |  | 4 | B
 |  |  |  |  |  |  | 2 | C
 |  |  |  |  |  |  | 0 | D
 |  | 3c.2 Maîtrise écrite du sujet | Qualité du dossier : Contenu correct, concis, argumentation convaincante, voie présentée maîtrisée |  |  |  | 6 | A |  | FALSE
 |  |  |  |  |  |  | 4 | B
 |  |  |  |  |  |  | 2 | C
 |  |  |  |  |  |  | 0 | D
 |  | 3c.3 Validation du hardware | Les éventuelles modifs. après design sont présentées. Le hardware reçu est testé. Les nouvelles modifs éventuelles sont présentées |  |  |  | 6 | A |  | FALSE
 |  |  |  |  |  |  | 4 | B
 |  |  |  |  |  |  | 2 | C
 |  |  |  |  |  |  | 0 | D
 |  | 3c.4 Description du logiciel | Les fonctionnalités et les grandes lignes du logiciel sont expliquées. Tout protocole utilisé ou créé est décrit. |  |  |  | 6 | A |  | FALSE
 |  |  |  |  |  |  | 4 | B
 |  |  |  |  |  |  | 2 | C
 |  |  |  |  |  |  | 0 | D
 |  | 3c.5 Tests et mesures | ...permettant de valider le fonctionnement. |  |  |  | 6 | A |  | FALSE
 |  |  |  |  |  |  | 4 | B
 |  |  |  |  |  |  | 2 | C
 |  |  |  |  |  |  | 0 | D
 |  | 3c.6 Bilan du fonctionnement et conclusion | Un état des lieux est dressé. Il est exhaustif. La reprise du projet est possible. |  |  |  | 3 | A |  | FALSE
 |  |  |  |  |  |  | 2 | B
 |  |  |  |  |  |  | 1 | C
 |  |  |  |  |  |  | 0 | D
 |  | 3c.7 Présentation des annexes | Qualité et exactitude des annexes (notamment : CDC dossier CAO, liste de pièces, coût réels, parties essentielles du code, planning initial et tâches effectives, journal de travail, mode d'emploi du système, résumé du projet, affiche du projet) |  |  |  | 3 | A |  | FALSE
 |  |  |  |  |  |  | 2 | B
 |  |  |  |  |  |  | 1 | C
 |  |  |  |  |  |  | 0 | D
 |  | Remarques | 3c.1 3c.2 3c.3 3c.4 3c.5 3c.6 3c.7
N° | Partie évaluée | Compétence | Indicateur / Critère de réussite |  | Evaluation A, B, C, D |  |  |  |  | Indicateur valide | Nbre pts max | Nbre pts compétence obtenus | Nbre pts compétence maximum | Pourcentage de compétence
4 | Présentation finale | 4.1 Capacité à présenter un sujet par oral | Expression : Le candidat s'exprime clairement, avec le bon langage. Compréhension aisée Qualité de la présentation : Moyens utilisés de manière appropriée, temps respecté |  |  |  | 3 | A |  | FALSE |  | 0 | 0 | #DIV/0!
 |  |  |  |  |  |  | 2 | B
 |  |  |  |  |  |  | 1 | C
 |  |  |  |  |  |  | 0 | D
 |  | 4.2 Maîtrise orale du sujet | Contenu technique : Contenu correct, synthétisé, concis, niveau adapté, argumentation convaincante, voie maîtrisée Réponses aux questions : Le candidat répond clairement et correctement aux questions |  |  |  | 6 | A |  | FALSE
 |  |  |  |  |  |  | 4 | B
 |  |  |  |  |  |  | 2 | C
 |  |  |  |  |  |  | 0 | D
 |  | 4.3 Démonstration | Démonstration claire et adéquate. Couvre le sujet et démontre les fonctionnalités/possibilités du projet. |  |  |  | 3 | A |  | FALSE
 |  |  |  |  |  |  | 2 | B
 |  |  |  |  |  |  | 1 | C
 |  |  |  |  |  |  | 0 | D
 |  | Remarques | 4.1 4.2 4.3
N° | Partie évaluée | Compétence | Indicateur / Critère de réussite |  | Evaluation A, B, C, D |  |  |  |  | Indicateur valide | Nbre pts max | Nbre pts compétence obtenus | Nbre pts compétence maximum | Pourcentage de compétence
5 | Attitude | 5.1 Conscience professionelle | Engagement, assiduité, volonté : horaires de travail et délais respectés, taux de présence, productivité telle qu'attendue, attitude générale positive, proactive |  |  |  | 3 | A |  | FALSE |  | 0 | 0 | #DIV/0!
 |  |  |  |  |  |  | 2 | B
 |  |  |  |  |  |  | 1 | C
 |  |  |  |  |  |  | 0 | D
 |  | 5.2 Organisation | Structuration du projet : cheminement logique du travail, travail ordonné Ordre, propreté, rangement : place de travaill ordonnée, aidant à l'avance du projet |  |  |  | 3 | A |  | FALSE
 |  |  |  |  |  |  | 2 | B
 |  |  |  |  |  |  | 1 | C
 |  |  |  |  |  |  | 0 | D
 |  | 5.3 Prise en compte des aspects de développement durable | Comportements et réalisations adaptés en fonction de critères écologiques, économiques et sociaux. Réflexion sur l'impact environnemental, économique ou social du produit et de son développement. |  |  |  | 3 | A |  | FALSE
 |  |  |  |  |  |  | 2 | B
 |  |  |  |  |  |  | 1 | C
 |  |  |  |  |  |  | 0 | D
 |  | Remarques | 5.1 5.2 5.3
Remarques générales
 |  |  |  |  |  |  |  |  | TOTAL de pts :
 |  |  |  |  |  |  |  |  | Sur un total de :
 |  |  |  |  |  |  |  |  | Note (0,1) : |  |  | #VALUE!
